chrkir/hcv/images/IMG_1100.PNG

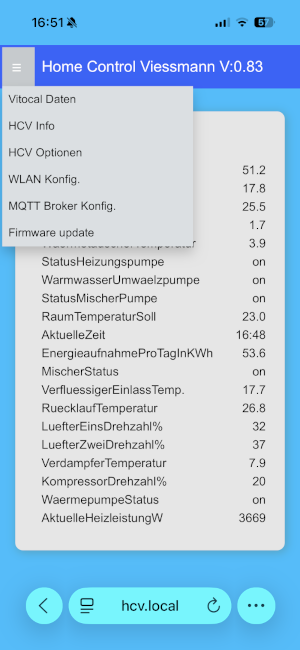
images/IMG_1100.PNG
